badenbaden/Waterius-Attiny84-ESP12F/ESP8266Flasher/параметры.png

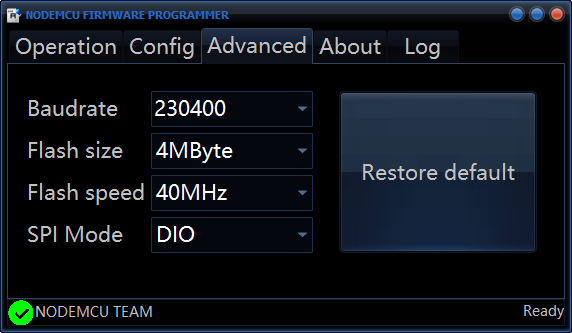
ESP8266Flasher/параметры.png
