badenbaden/Waterius-Attiny84-ESP12F/Foto/Bottom.jpg

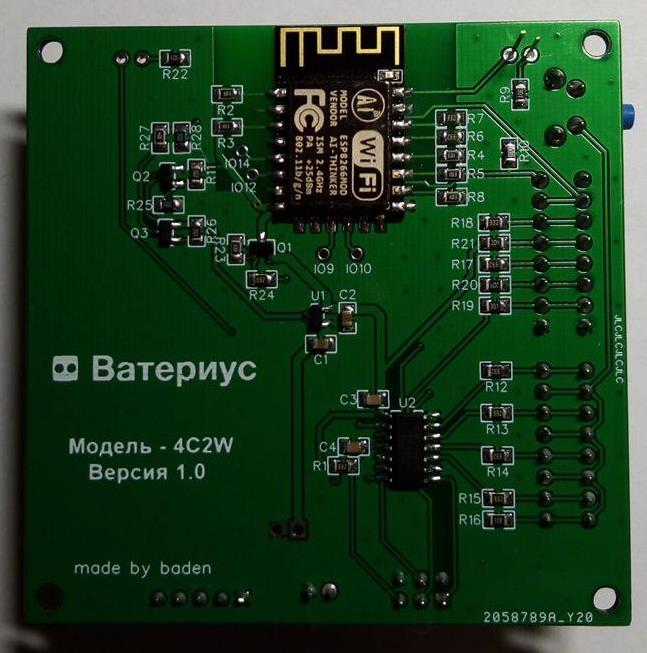
Foto/Bottom.jpg
