badenbaden/Waterius-Attiny84-ESP12F/Foto/Top.jpg

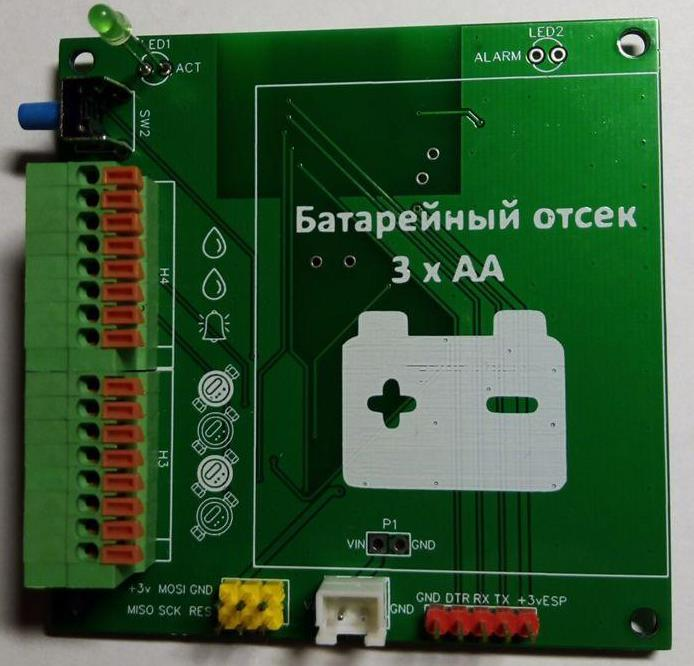
Foto/Top.jpg
