badenbaden/Waterius-Attiny84-ESP12F/Foto/В корпусе 1.jpg

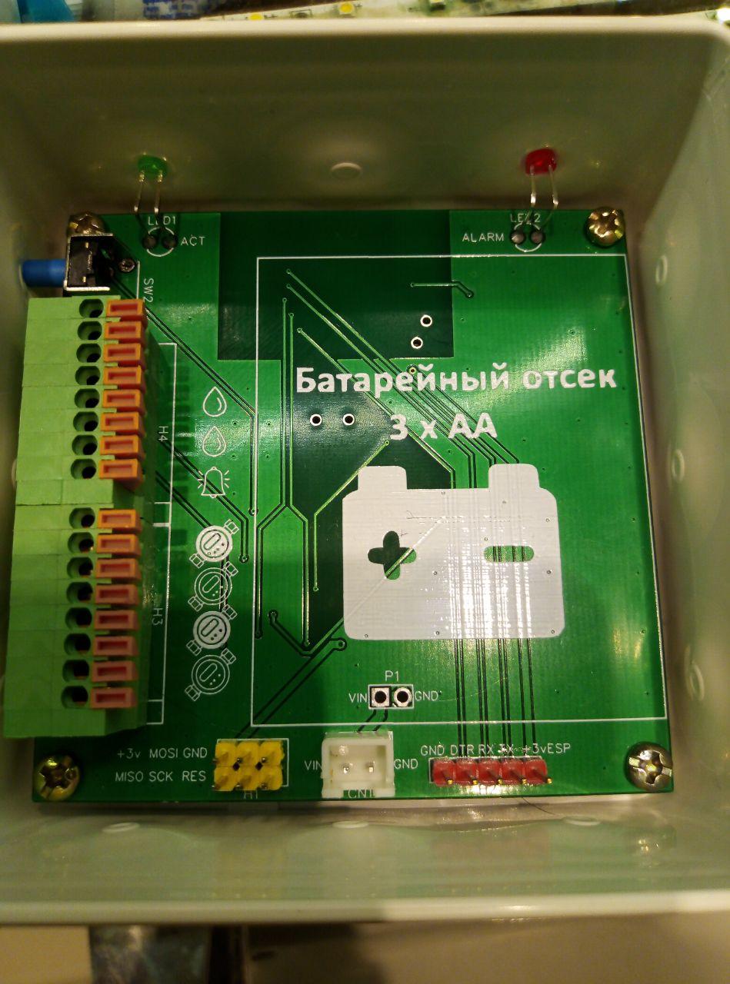
Foto/В корпусе 1.jpg
