badenbaden/Waterius-Attiny84-ESP12F/Foto/В корпусе 5.jpg

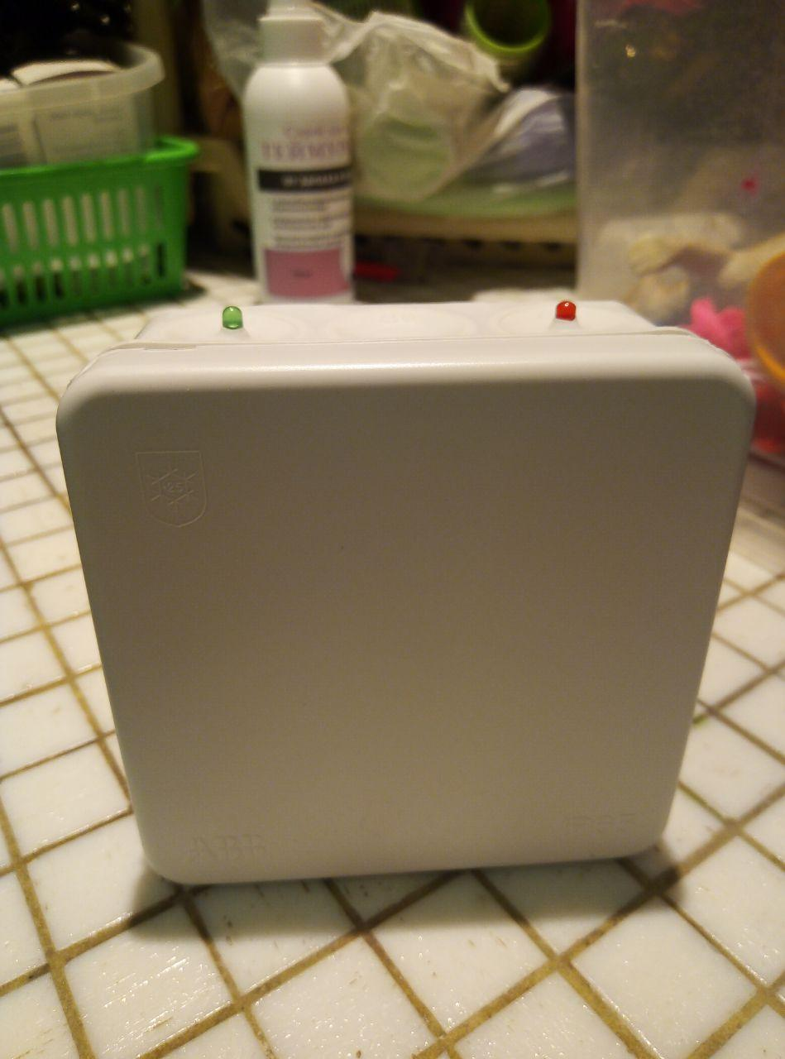
Foto/В корпусе 5.jpg
