badenbaden/Waterius-Attiny84-ESP12F/Foto/В корпусе 6.jpg

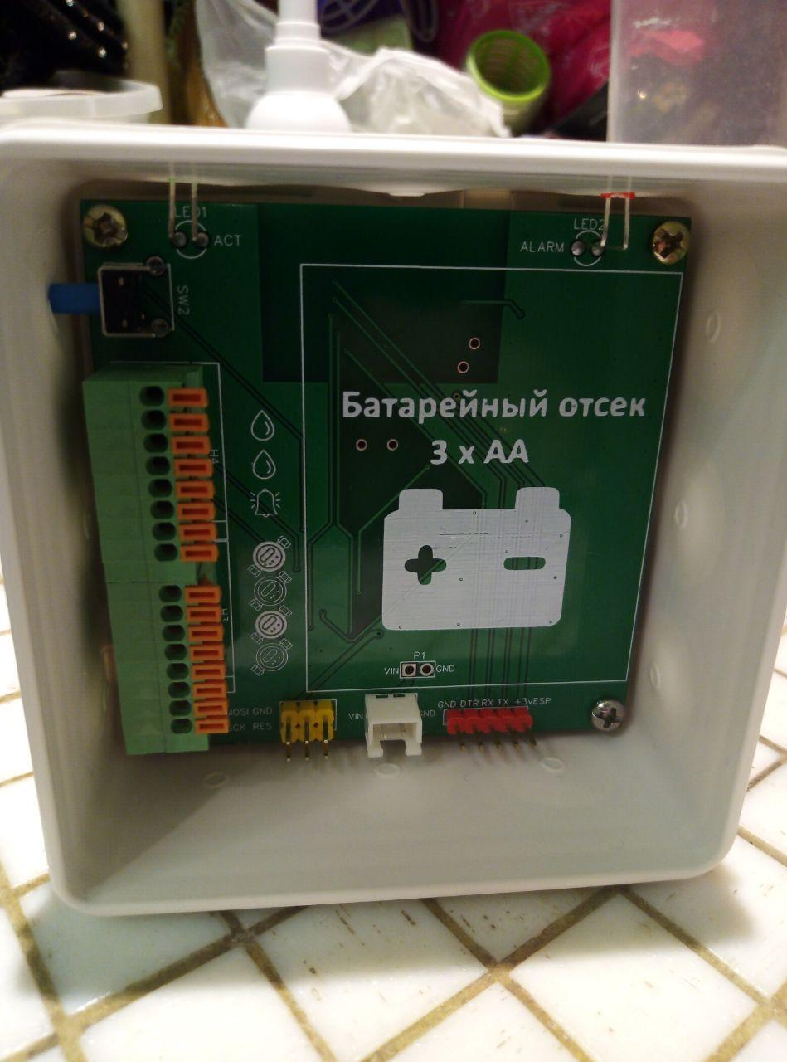
Foto/В корпусе 6.jpg
