badenbaden/Waterius-Attiny84-ESP12F/Foto/Корпус 1.jpg

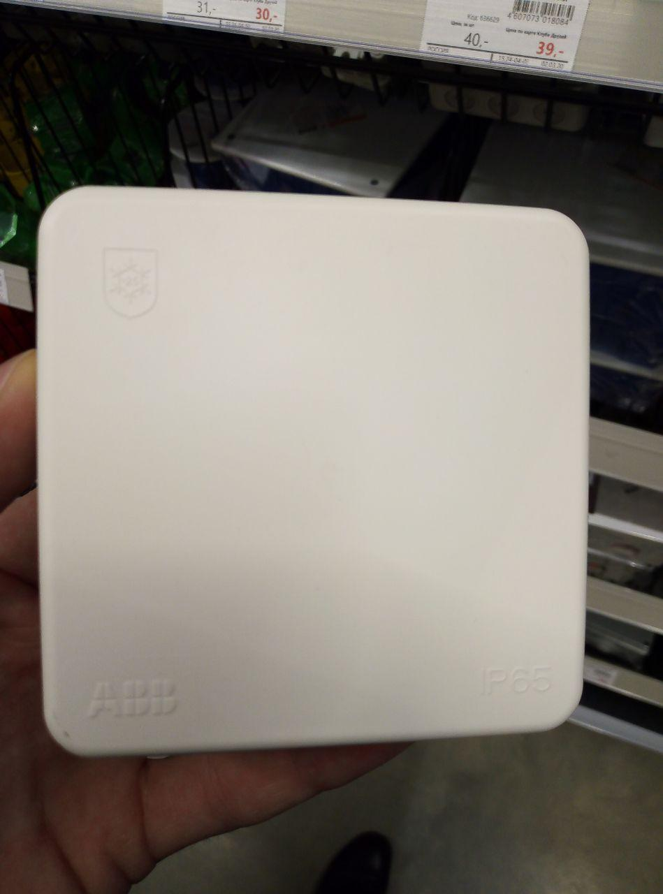
Foto/Корпус 1.jpg
