badenbaden/Waterius-Attiny84-ESP12F/Foto/Корпус 2.jpg

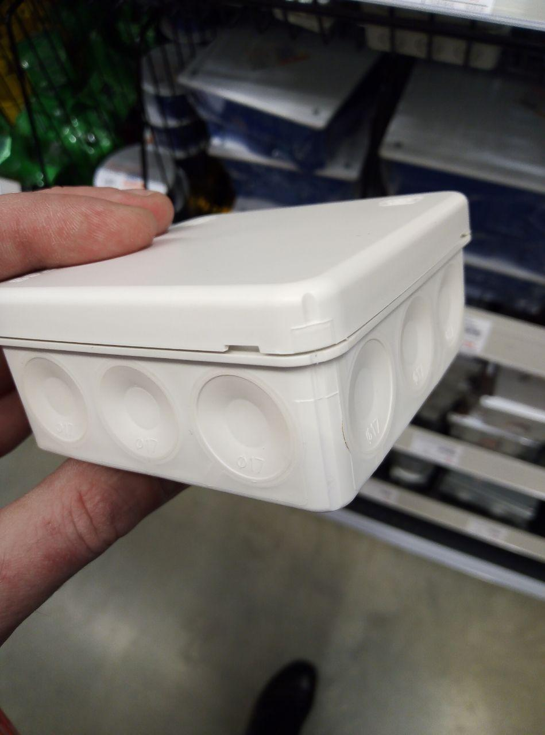
Foto/Корпус 2.jpg
