badenbaden/Waterius-Attiny84-ESP12F/Foto/Корпус 3.jpg

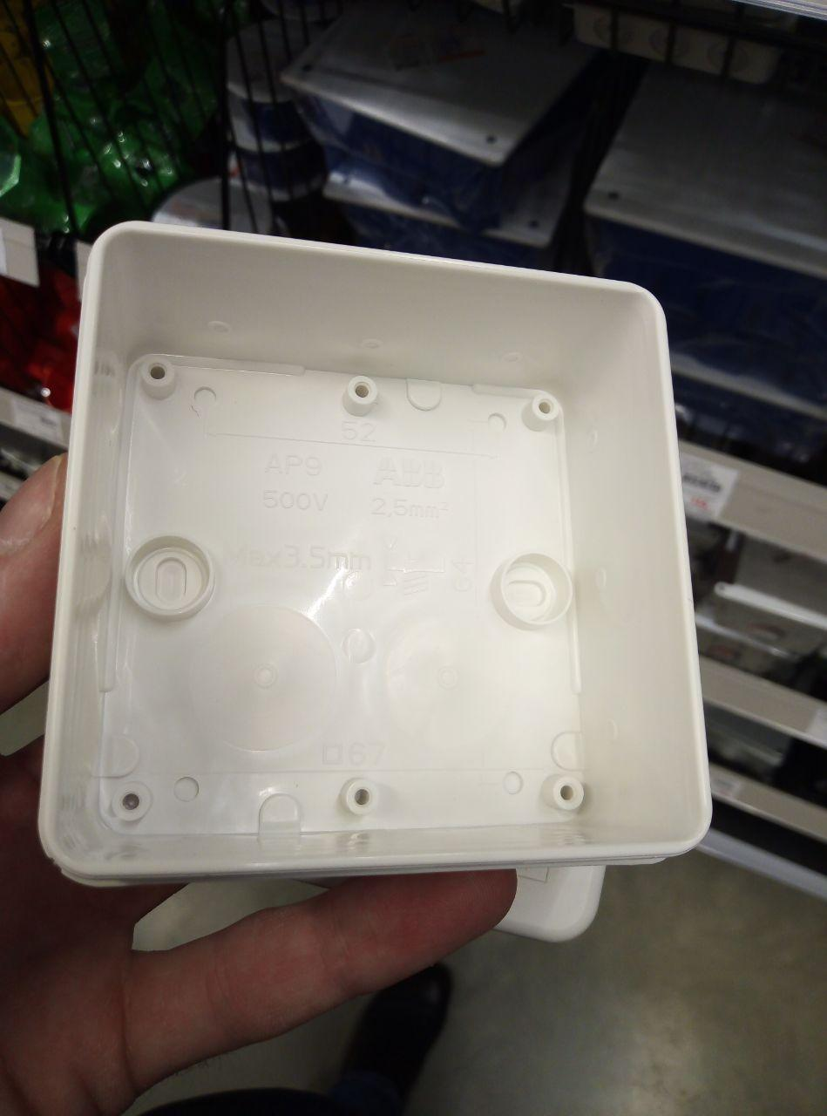
Foto/Корпус 3.jpg
