badenbaden/Waterius-Attiny84-ESP12F/Others/alarm.png

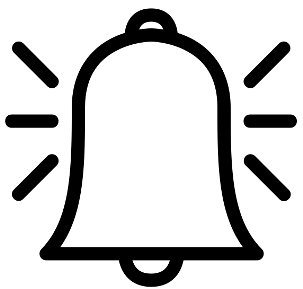
Others/alarm.png
