badenbaden/Waterius-Attiny84-ESP12F/Others/battery.png

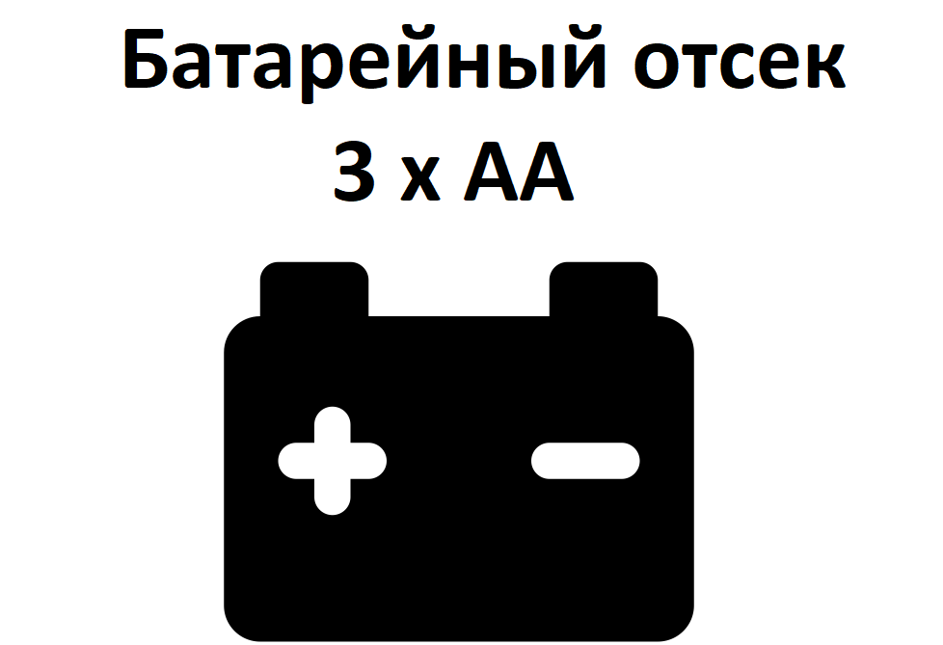
Others/battery.png
