badenbaden/Waterius-Attiny84-ESP12F/Others/горячая.png

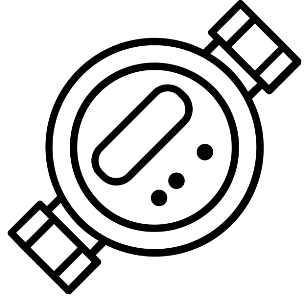
Others/горячая.png
