badenbaden/Waterius-Attiny84-ESP12F/Simulation/Mosfet-off.png

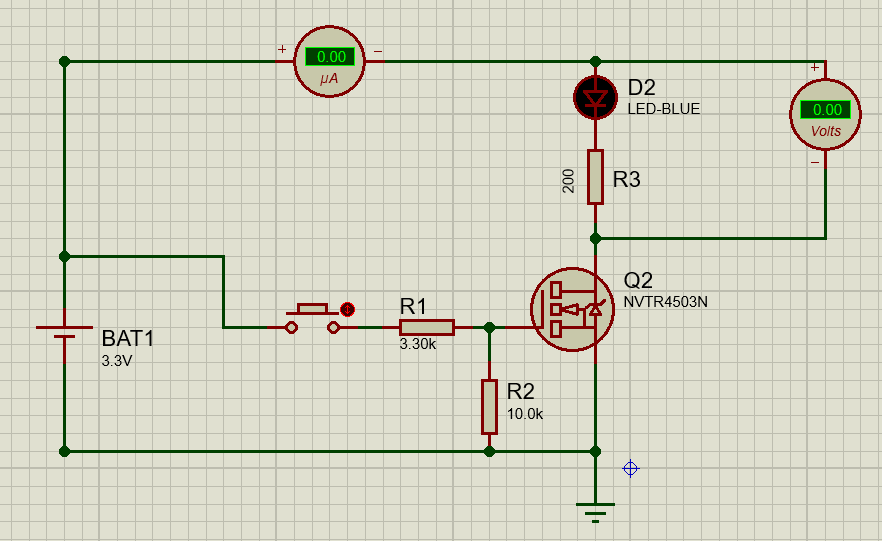
Simulation/Mosfet-off.png
