badenbaden/Waterius-Attiny84-ESP12F/Simulation/Mosfet-on.png

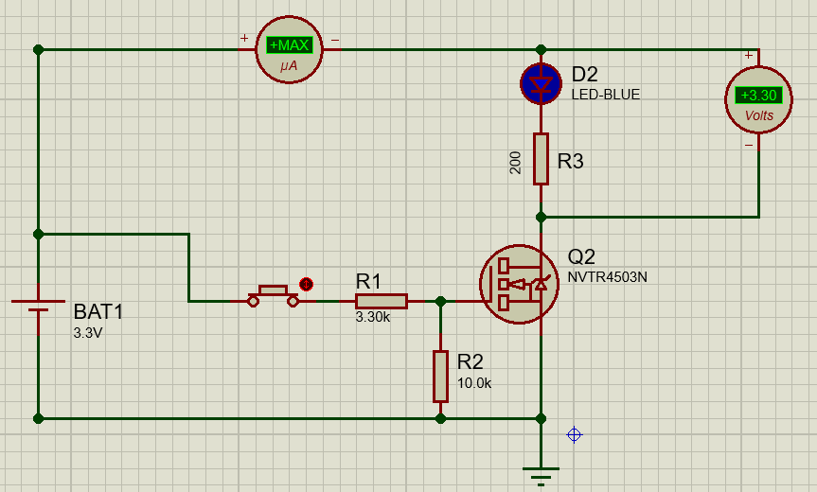
Simulation/Mosfet-on.png
