badenbaden/Waterius-Attiny84-ESP12F/Simulation/photo_2020-04-05_20-48-12.jpg

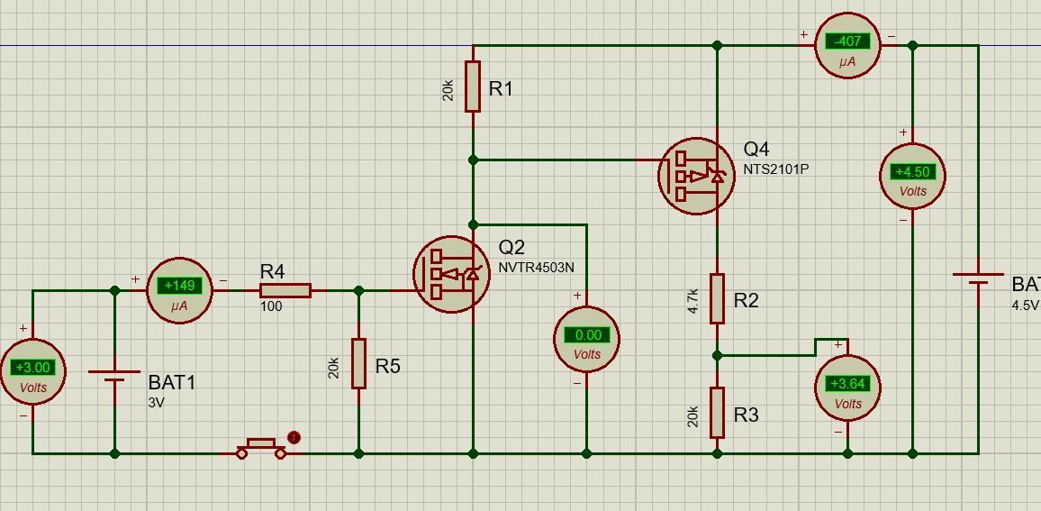
Simulation/photo_2020-04-05_20-48-12.jpg
