badenbaden/Waterius-Attiny84-ESP12F/SinaProg 2.1.1/data/SinaProg.png

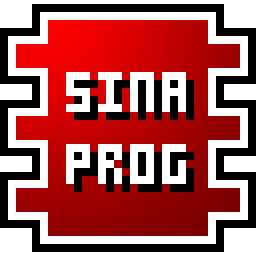
SinaProg 2.1.1/data/SinaProg.png
