badenbaden/Waterius-Attiny84-ESP12F/Visualization/abb-ap9.jpg

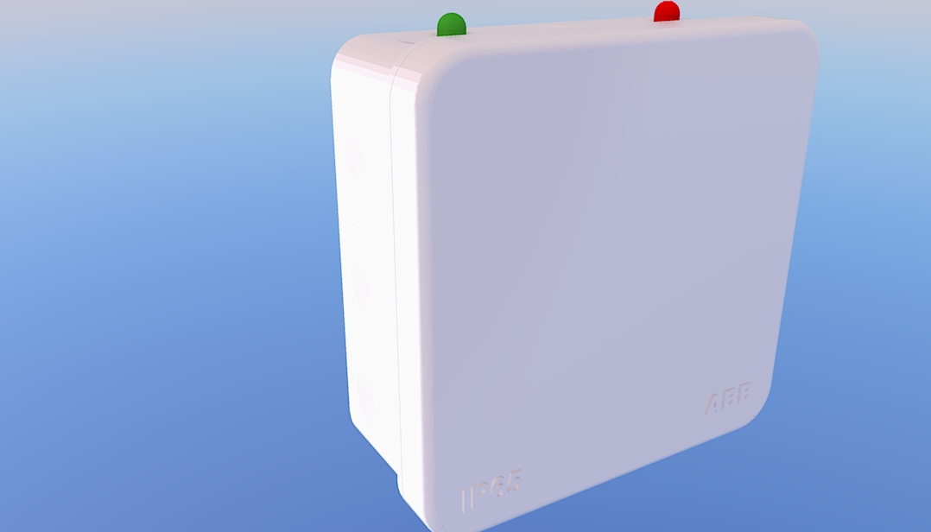
Visualization/abb-ap9.jpg
