badenbaden/Waterius-Attiny84-ESP12F/Visualization/рендер-низ2.jpg

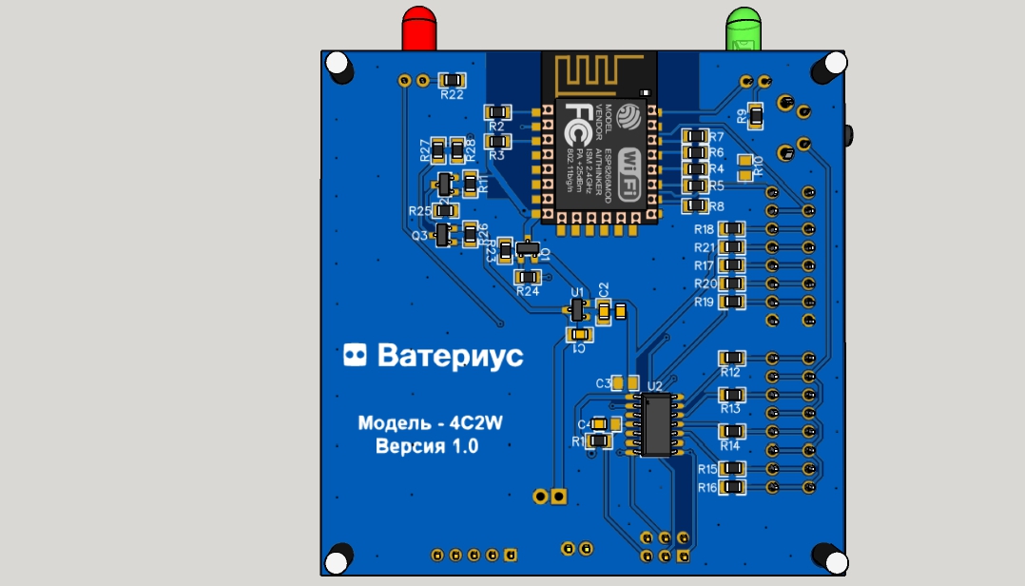
Visualization/рендер-низ2.jpg
