badenbaden/Waterius-Attiny84-ESP12F/Сircuit/voltage_divider.jpg

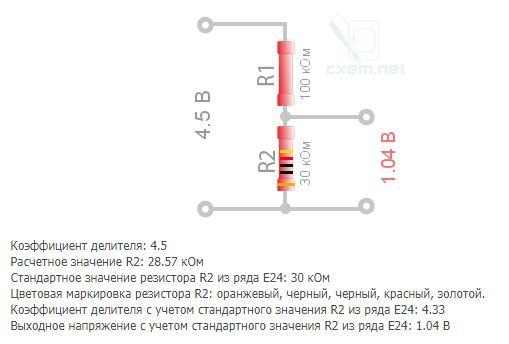
Сircuit/voltage_divider.jpg
